zUrp-Astronomics/Maelstrom/1_Board/Logic-board/Maelstrom-Logic-board-v1.1_2-view_bot.png

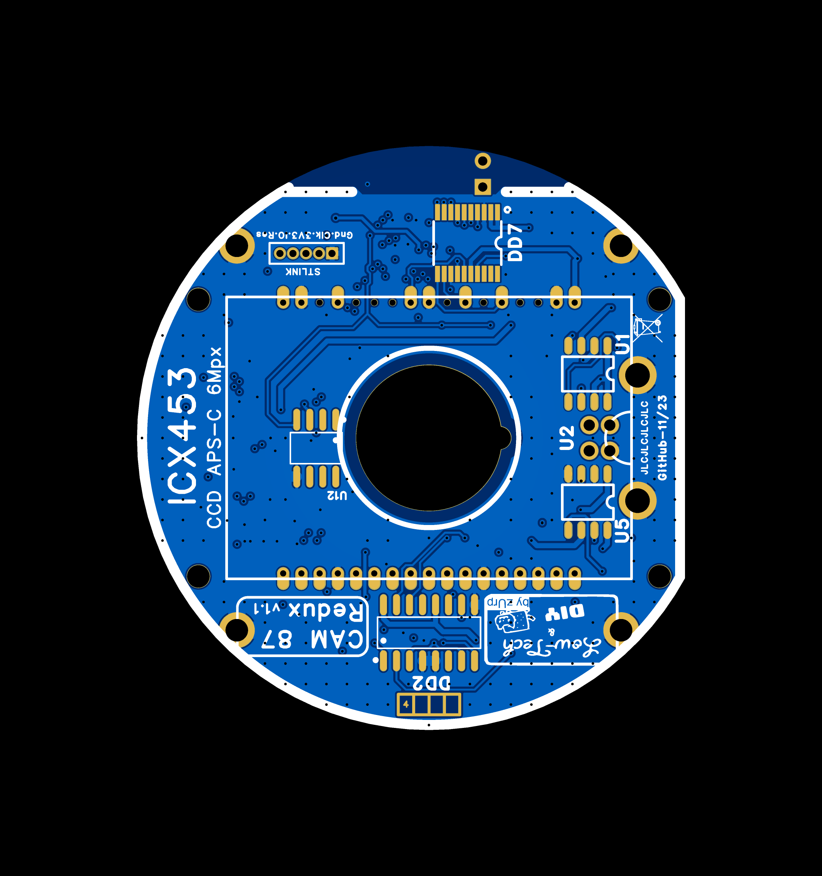
1_Board/Logic-board/Maelstrom-Logic-board-v1.1_2-view_bot.png
