zUrp-Astronomics/Maelstrom/1_Board/Power-board/Maelstrom-Power-board-v1.1_2-view_bot.png

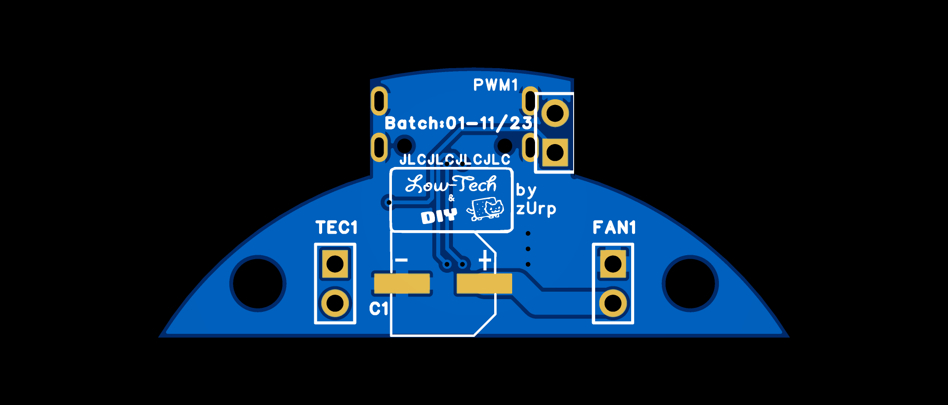
1_Board/Power-board/Maelstrom-Power-board-v1.1_2-view_bot.png
